OpenLicht/GlowingCup/Benutzte Apps.PNG

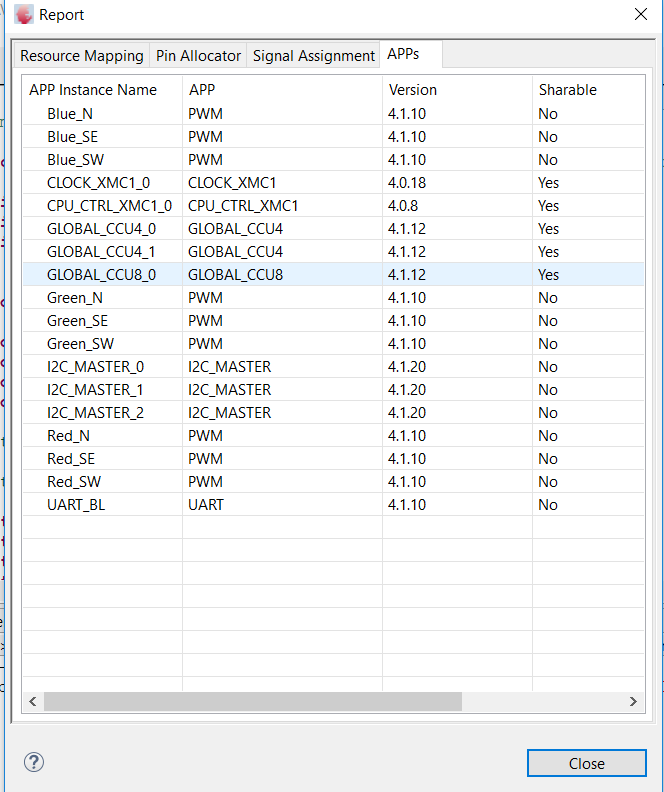
Benutzte Apps.PNG
